kevin-allen/laserController/Actuator_marcel_edition/sliderBelt.stl

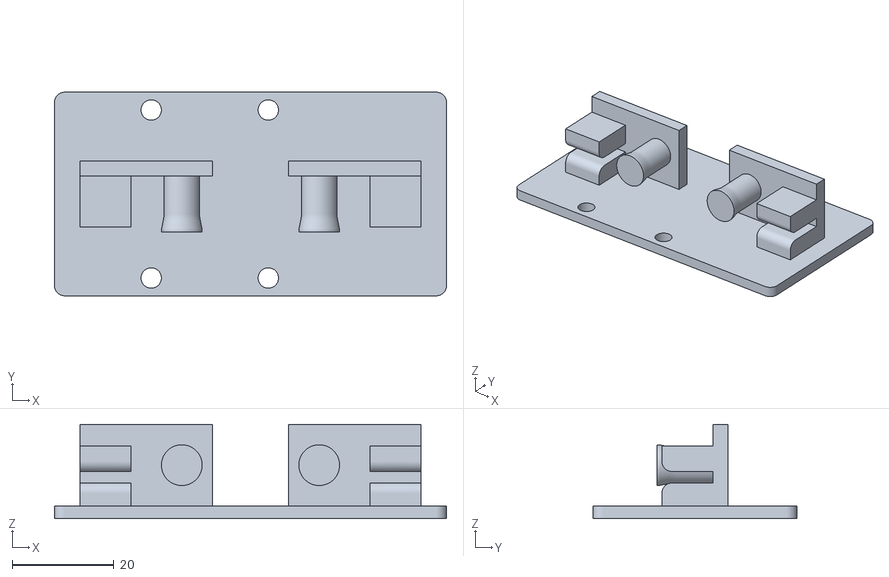
[picture p15: CAD file, 2023-06-23]
Actuator_marcel_edition/sliderBelt.stl
77.0 x 40.0 x 18.5
