kevin-allen/laserController/Actuator_marcel_edition/MiddleTop.stl

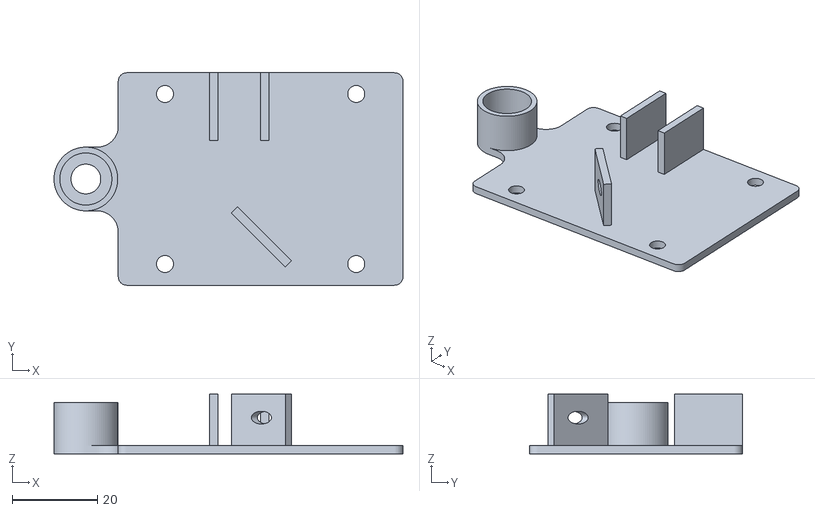
[picture p16: CAD file, 2023-06-23]
Actuator_marcel_edition/MiddleTop.stl
82.1 x 50.0 x 14.0
